jstwy/CMX_K_Six-key/CMX_K_Six-key.Firmware/led.c

/*
 * Original firmware files: Copyright 2012 Jun Wako <wakojun@gmail.com>, <github.com/tmk/tmk_keyboard>
 */

#include "stdint.h"
#include "led.h"

/* No LEDs on CMX K Six-key */
void led_set(uint8_t usb_led)
{
}
